drollette/W7HAK-gobox/pcb/w7hak_hat/w7hak_hat.kicad_sch

## KiCad design pcb/w7hak_hat/w7hak_hat.kicad_sch (2026-04-01)

Schematic: w7hak_hat.kicad_sch

Parts:
C: C_Polarized
J: Conn_01x05
R: R

Notes on the sheet:
W7HAK Go-Box: Pi Zero W Telemetry HAT This HAT sits on the Pi Zero W 40-pin GPIO header and provides: - JST-XH 5-pin connector (J1) for BMS battery cell taps + ground - JST-XH 6-pin connector (J2) for ADS1115 ADC module - 4-channel resistor ladder voltage dividers (1% precision) - Hardware RC low-p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
DESIGN NOTES: - All divider & filter resistors are 1% precision metal film - All capacitors rated minimum 25V (LiFePO4 pack reaches 14.6V) - RC filter cutoff: f = 1/(2π×1kΩ×10µF) ≈ 16 Hz - Board dimensions: 65mm × 30mm (Pi Zero HAT form factor) - Mount with 2x20 pin female header (pin 1 aligned wit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
